fbutkovich/Smart-Buck-Intelligent-DC-DC-Converter/docs/assets/images/IMG_2853.JPG

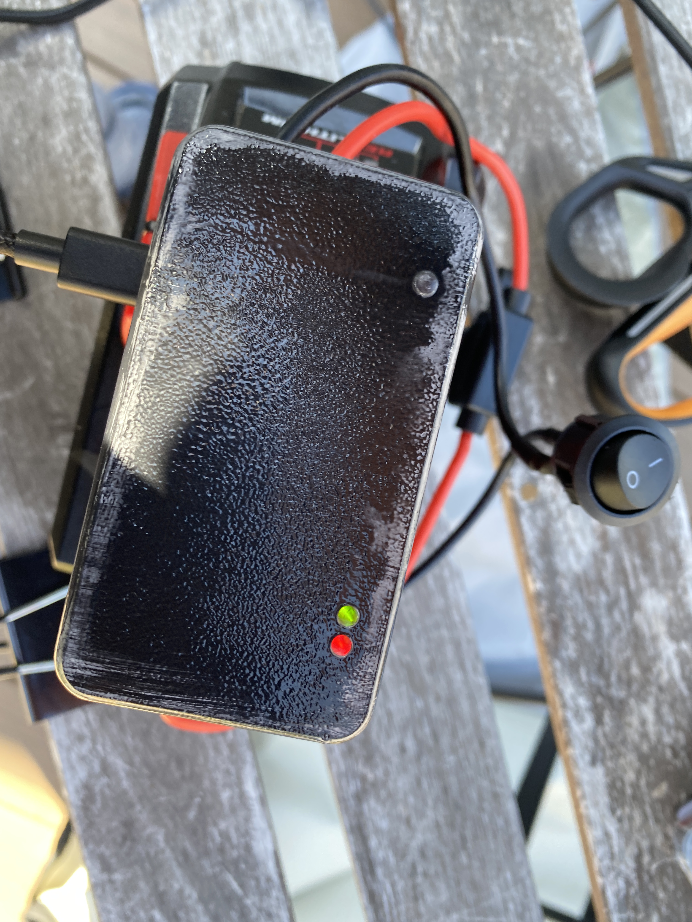
docs/assets/images/IMG_2853.JPG
